redaphid/nfc-bead/beads/filibertos-taco/print/neon/DecorationSilhouette.stl

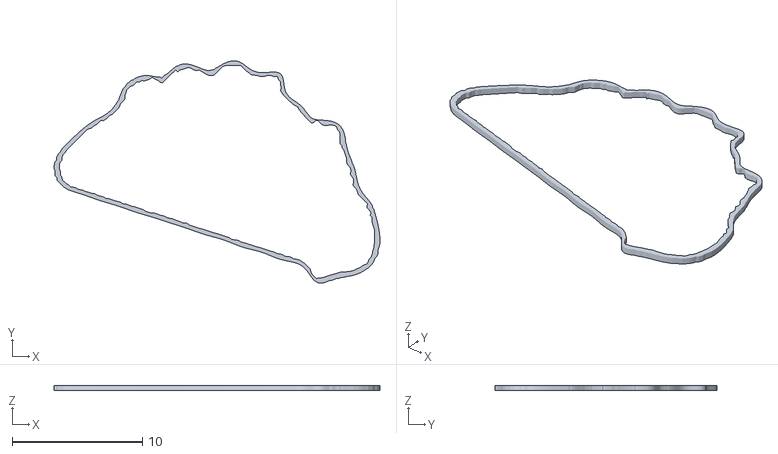
[picture p18: CAD file, 2026-05-09]
beads/filibertos-taco/print/neon/DecorationSilhouette.stl
25.0 x 17.0 x 0.4
