redaphid/nfc-bead/beads/redaphid-portrait-v2/print/Hair.stl

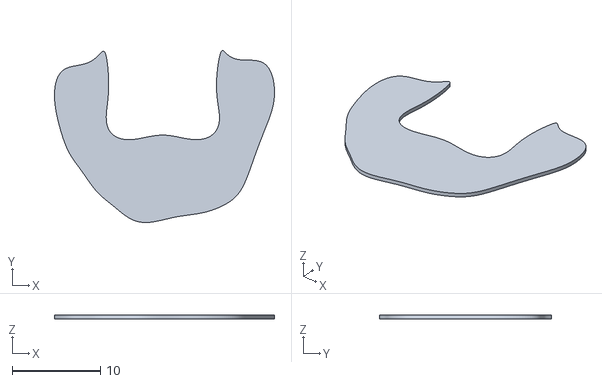
[picture p19: CAD file, 2026-06-21]
beads/redaphid-portrait-v2/print/Hair.stl
25.0 x 19.5 x 0.4
