redaphid/nfc-bead/beads/filibertos-taco/print/blocks/DecorationInteriorDetail.stl

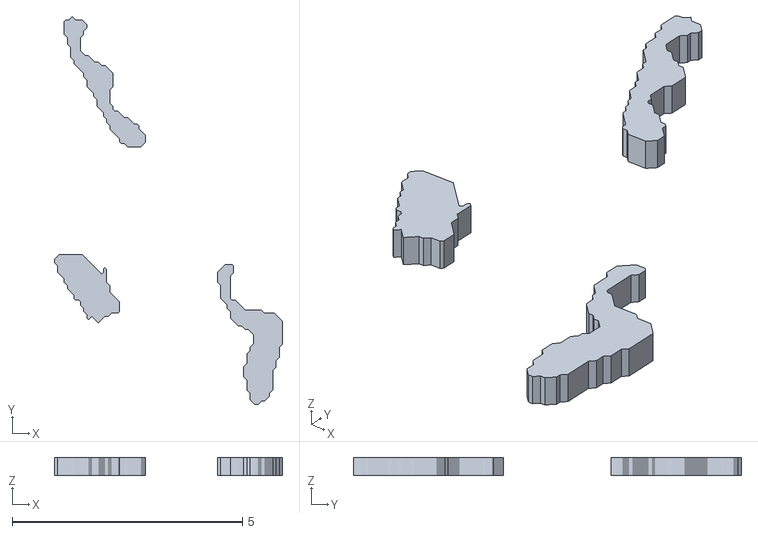
[picture p20: CAD file, 2026-05-09]
beads/filibertos-taco/print/blocks/DecorationInteriorDetail.stl
4.96 x 8.43 x 0.4
