redaphid/nfc-bead/beads/filibertos-taco/print/Decoration.stl

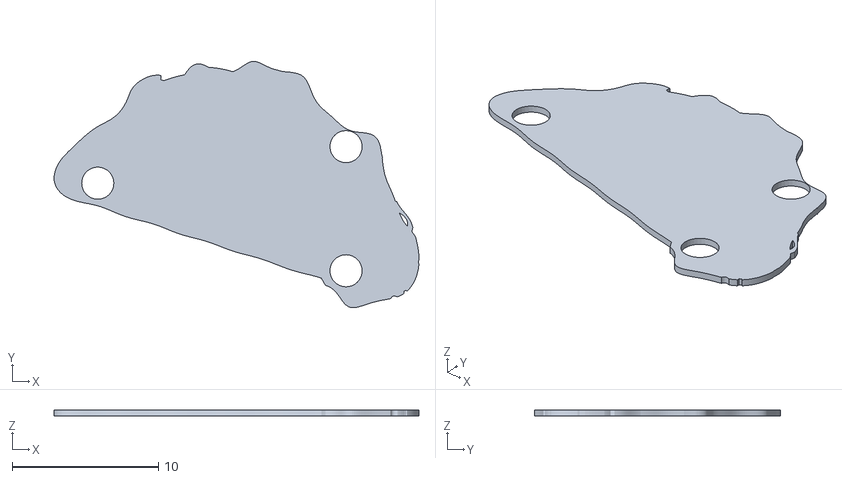
[picture p21: CAD file, 2026-05-09]
beads/filibertos-taco/print/Decoration.stl
25.0 x 16.9 x 0.4
