redaphid/nfc-bead/beads/filibertos-taco/print/neon/filibertos-taco-neon.3mf

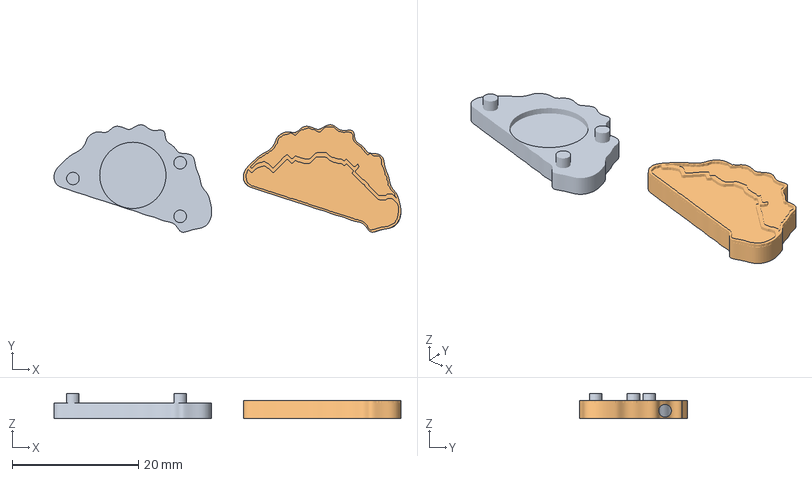
[picture p22: CAD file, 2026-05-09]
beads/filibertos-taco/print/neon/filibertos-taco-neon.3mf
55.0 x 17.0 x 4.00 mm
Bottom
Top_with_Decoration
