redaphid/nfc-bead/beads/redaphid-portrait-v2/print/redaphid-portrait-v2.3mf

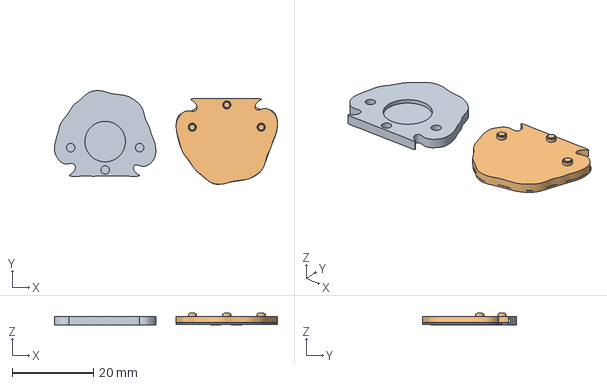
[picture p23: CAD file, 2026-06-21]
beads/redaphid-portrait-v2/print/redaphid-portrait-v2.3mf
55.0 x 23.1 x 2.86 mm
Bottom
Top_with_Decoration_and_Hair
