redaphid/nfc-bead/beads/filibertos-taco/print/DecorationLettuceDark.stl

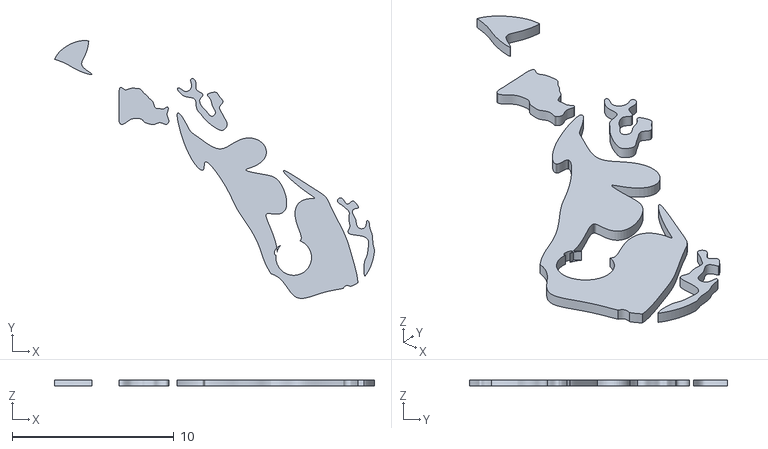
[picture p24: CAD file, 2026-05-09]
beads/filibertos-taco/print/DecorationLettuceDark.stl
19.8 x 15.9 x 0.4
