redaphid/nfc-bead/beads/filibertos-taco/print/blocks/DecorationLettuceSeparator.stl

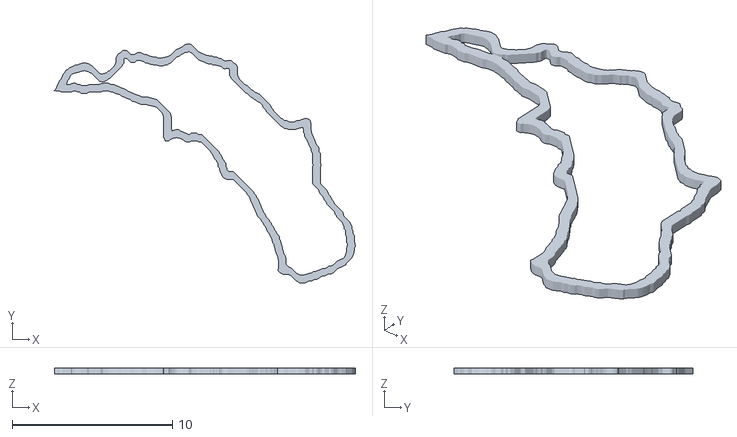
[picture p25: CAD file, 2026-05-09]
beads/filibertos-taco/print/blocks/DecorationLettuceSeparator.stl
18.8 x 14.9 x 0.4
