redaphid/nfc-bead/beads/filibertos-taco/print/DecorationLettuceLight.stl

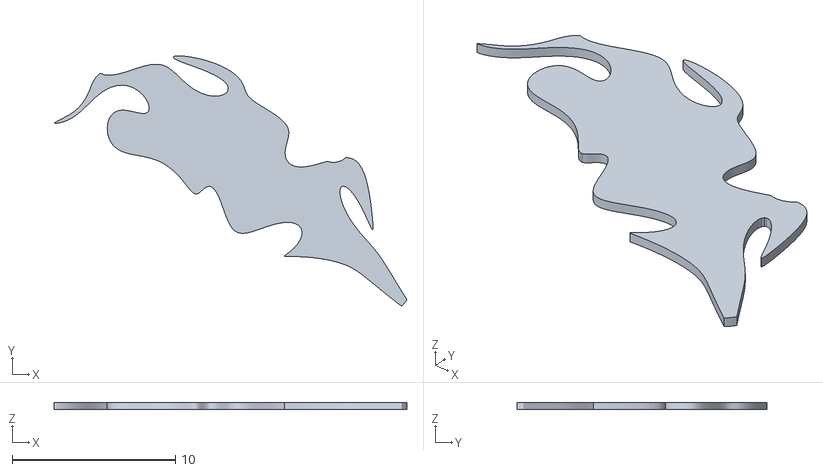
[picture p26: CAD file, 2026-05-09]
beads/filibertos-taco/print/DecorationLettuceLight.stl
21.6 x 15.3 x 0.4
